mcpiface/Status/V3/Images/PcbTopSilkAndValues.png

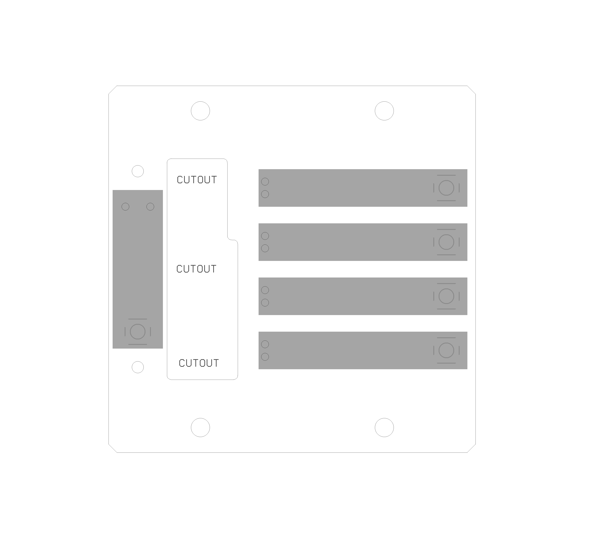
V3/Images/PcbTopSilkAndValues.png
