mcpiface/Status/V3/Images/I2C-Wiring-2.jpg

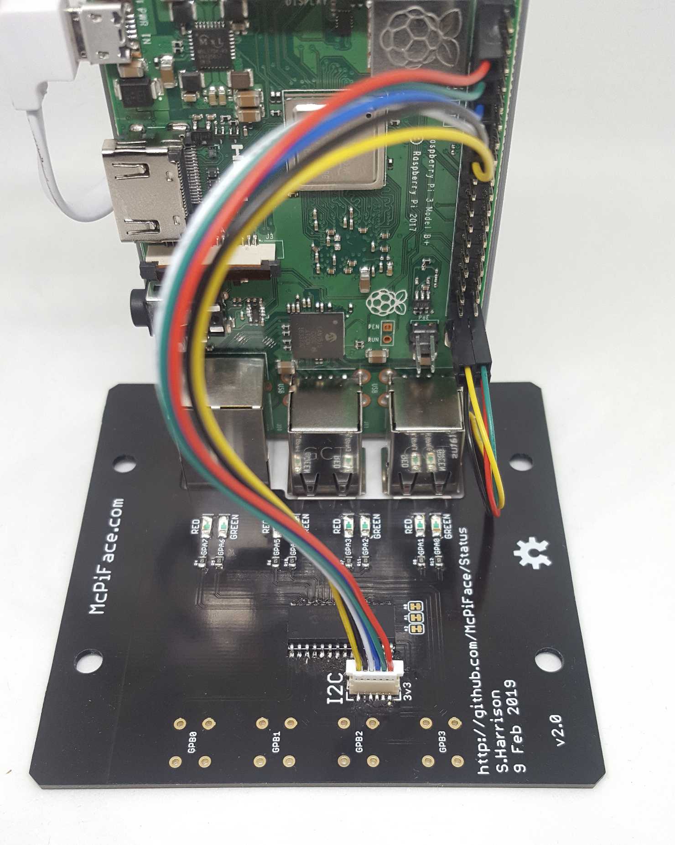
V3/Images/I2C-Wiring-2.jpg
